DIYSynthMNL/Eurorack-3330-Dual-Lin-Exp-VCA/kicad/Eurorack-AS3330-Dual-Lin-Exp-VCA.kicad_pcb

## KiCad design kicad-files/matterdoor.kicad_sch

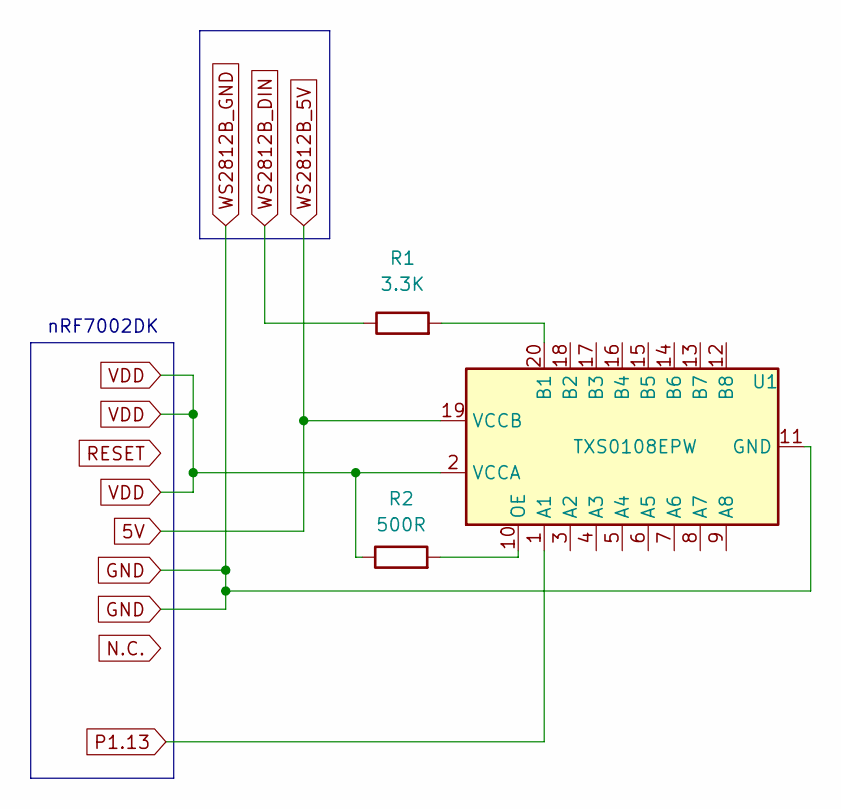
[picture p9: schematic matterdoor.kicad_sch]

Parts:
R1: 3.3K
R2: 500R
U1: TXS0108EPW; TSSOP-20_4.4x6.5mm_P0.65mm

Connections:
5V: U1.19 (VCCB)
GND: U1.11 (GND)
unnamed: R1.2, U1.20 (B1)
unnamed: R2.2, U1.10 (OE)
P1.13: U1.1 (A1)
VDD: R2.1, U1.2 (VCCA)
WS2812B_DIN: R1.1

Notes on the sheet:
nRF7002DK
